khinds10/CarTripComputer/status.py

#! /usr/bin/python
# Car Trip Computer - update screen status
# Kevin Hinds http://www.kevinhinds.com
# License: GPL 2.0
import time, commands, subprocess, re, json, sys, os, memcache, json
import datetime as dt
import includes.data as data
from gpiozero import Button
from datetime import datetime
mc = memcache.Client(["127.0.0.1:11211"], debug=0)

# begin the loop to get the current status to show on the display
mc.set("INUSE", "")
while True:
    try:
        # make sure there"s no other process using the screen by checking the memcache semaphore variable
        displayInUse = mc.get("INUSE")
        if displayInUse == "INUSE":
            print "display in use"
            time.sleep(1)
            continue
        mc.set("INUSE", "INUSE")
    
        # get current date and time
        timestamp = time.time()
        drivingStatus = data.getJSONFromFile("driving.json")
        lastUpdate = data.getModificationDate("driving.json")
        lastUpdateReadable = data.displayHumanReadableTime((int(timestamp)-int(lastUpdate)))
        
        if lastUpdateReadable == "":
            lastUpdateReadable = "0m"
        
        # clear previous entry
        subprocess.call(["/home/pi/CarTripComputer/digole", "setFont", "51"])        
        subprocess.call(["/home/pi/CarTripComputer/digole", "setColor", "0"])
        subprocess.call(["/home/pi/CarTripComputer/digole", "printxy_abs", "10", "200", "XXXXX"])
        subprocess.call(["/home/pi/CarTripComputer/digole", "printxy_abs", "40", "230", "XXXXX"])
        
        # show driving time
        if drivingStatus == "DRIVING":
            subprocess.call(["/home/pi/CarTripComputer/digole", "setColor", "189"])
            subprocess.call(["/home/pi/CarTripComputer/digole", "printxy_abs", "10", "200", "Driving"])
            subprocess.call(["/home/pi/CarTripComputer/digole", "printxy_abs", "40", "230", str(lastUpdateReadable)])

        # show idle time
        if drivingStatus == "IDLE":
            subprocess.call(["/home/pi/CarTripComputer/digole", "setColor", "245"])
            subprocess.call(["/home/pi/CarTripComputer/digole", "printxy_abs", "10", "200", "Idle"])
            subprocess.call(["/home/pi/CarTripComputer/digole", "printxy_abs", "40", "230", str(lastUpdateReadable)])

        # turn off the in use flag for the screen, we"re done writing to it
        mc.set("INUSE", "")

        # wait 1 second
        time.sleep(10)

    except (Exception):
        # Network or other issue, wait 1 second
        mc.set("INUSE", "")
        time.sleep(10)
